zukaitis/midi-grid/Images/firmware_structure.png

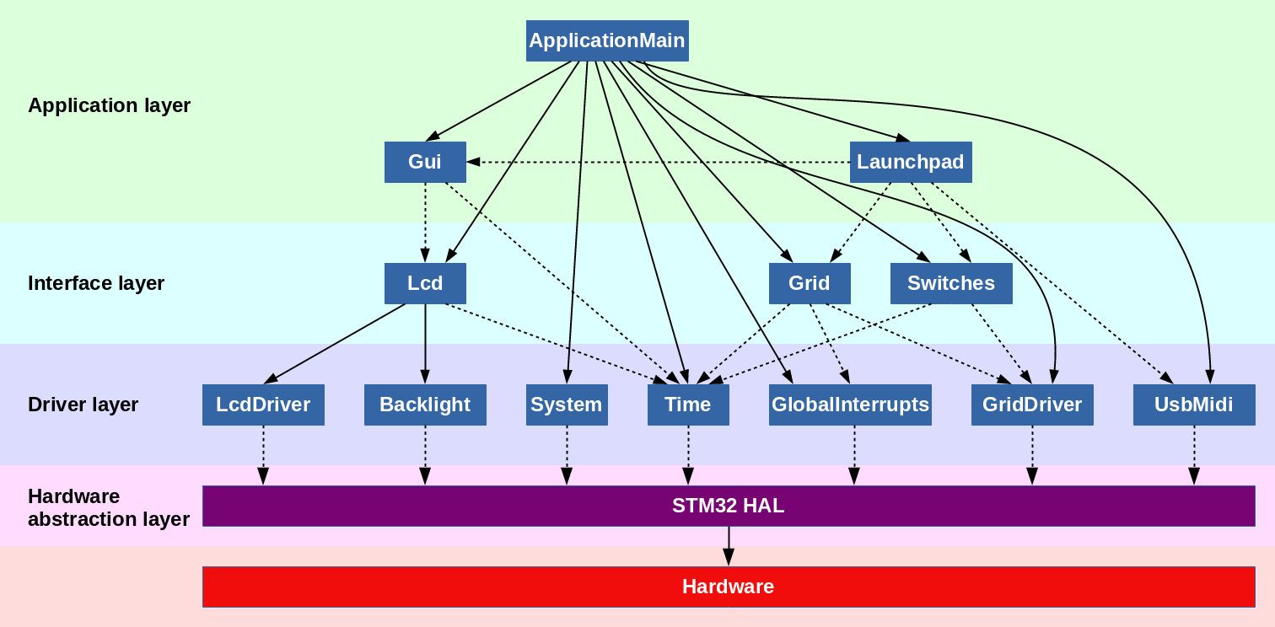
Images/firmware_structure.png
