zukaitis/midi-grid/Images/live_photo_2.jpg

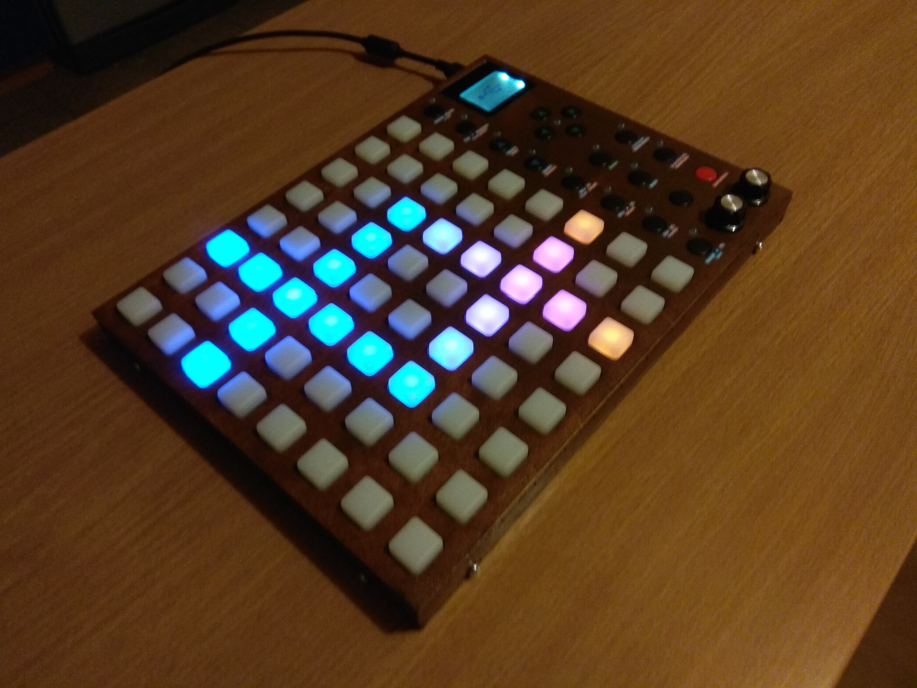
Images/live_photo_2.jpg
