zukaitis/midi-grid/Images/live_photo_3.jpg

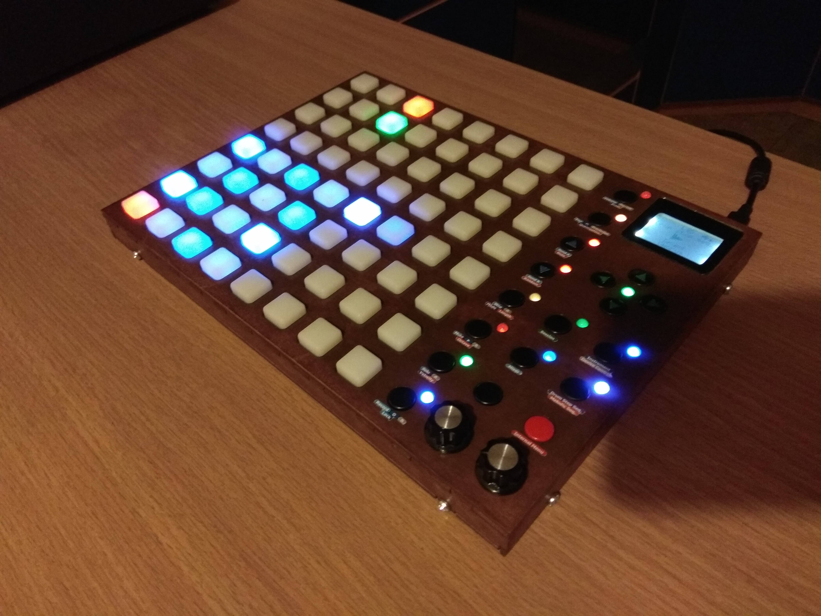
Images/live_photo_3.jpg
