zukaitis/midi-grid/Images/live_photo_5.jpg

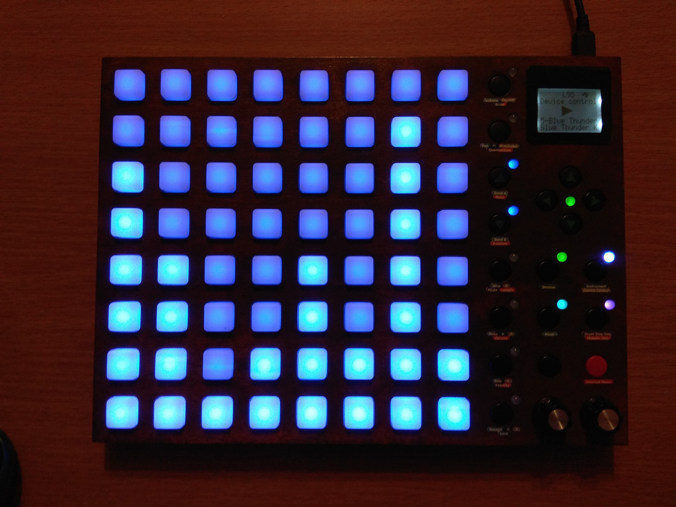
Images/live_photo_5.jpg
