zukaitis/midi-grid/Images/live_photo_6.jpg

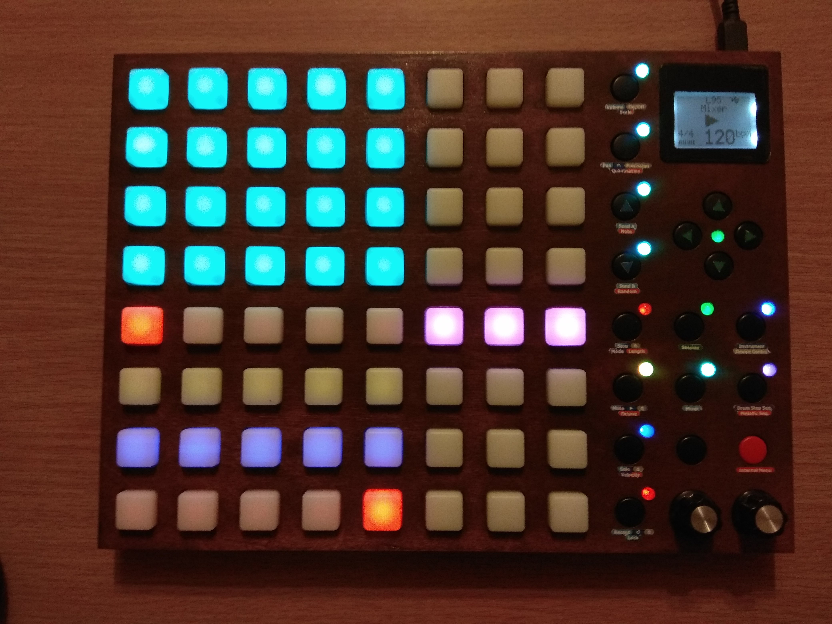
Images/live_photo_6.jpg
