zukaitis/midi-grid/Images/live_photo_7.jpg

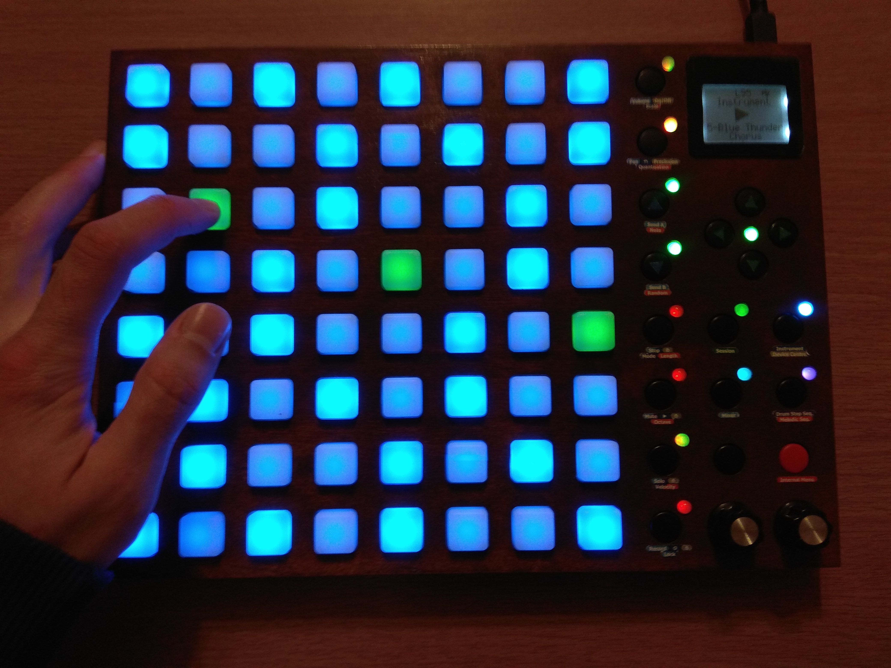
Images/live_photo_7.jpg
