zukaitis/midi-grid/Images/live_photo_9.jpg

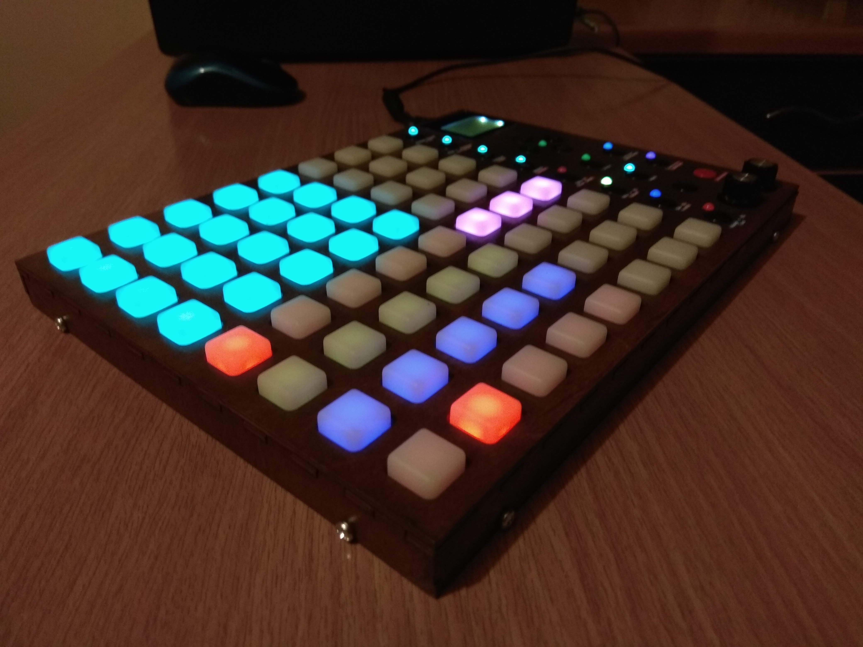
Images/live_photo_9.jpg
