zukaitis/midi-grid/Images/live_photo_10.jpg

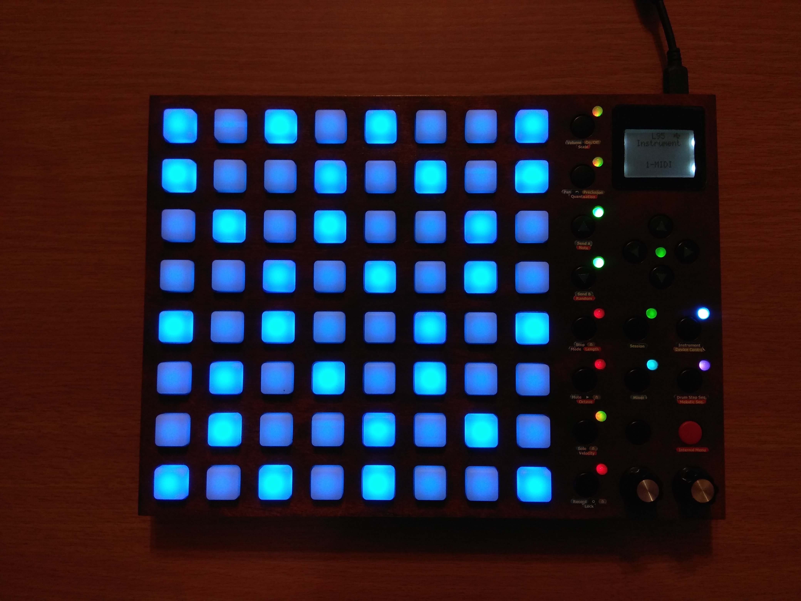
Images/live_photo_10.jpg
