zukaitis/midi-grid/Images/live_photo_11.jpg

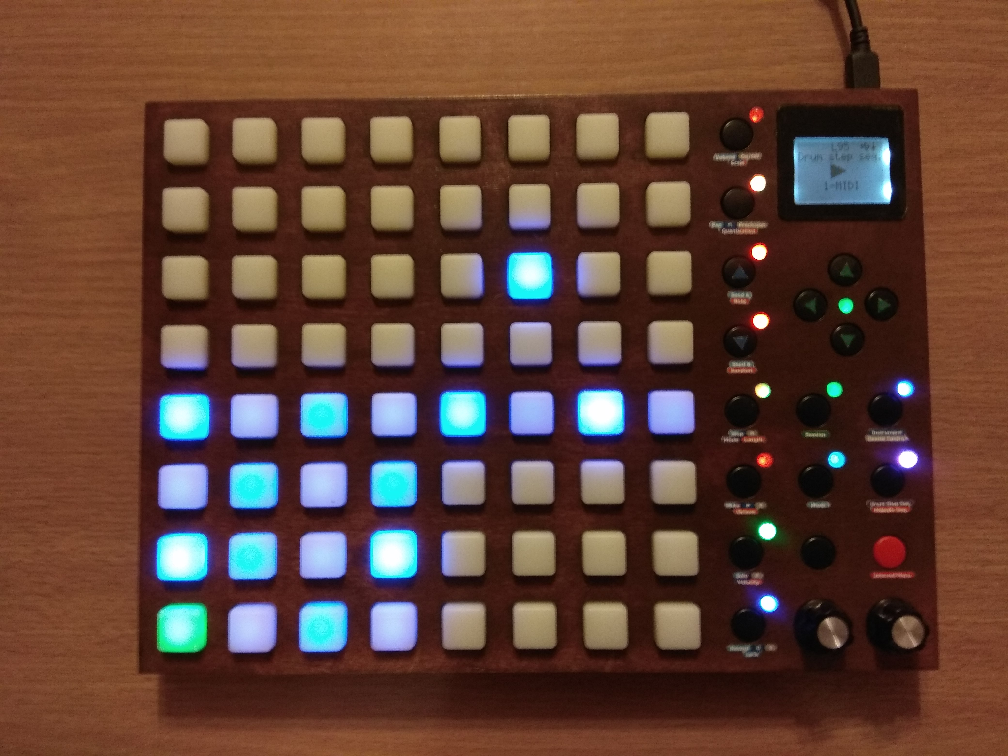
Images/live_photo_11.jpg
