zukaitis/midi-grid/Images/pcb_3d_render_front.png

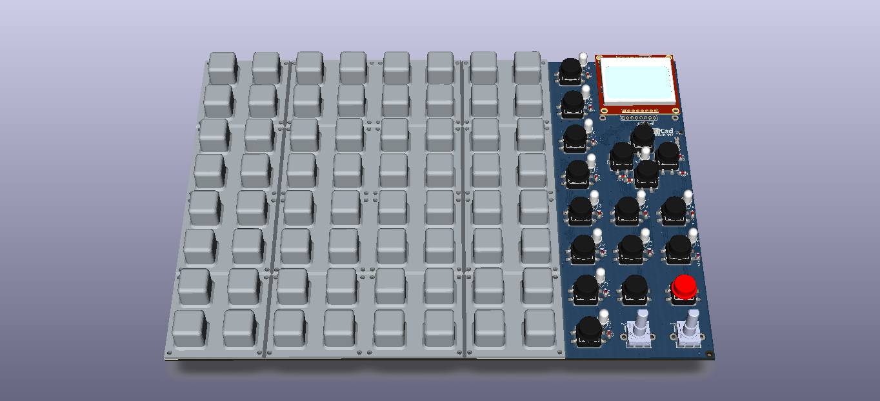
Images/pcb_3d_render_front.png
