zukaitis/midi-grid/Firmware/Src/main.c

/**
  ******************************************************************************
  * @file           : main.c
  * @brief          : Main program body
  ******************************************************************************
  * This notice applies to any and all portions of this file
  * that are not between comment pairs USER CODE BEGIN and
  * USER CODE END. Other portions of this file, whether 
  * inserted by the user or by software development tools
  * are owned by their respective copyright owners.
  *
  * Copyright (c) 2018 STMicroelectronics International N.V. 
  * All rights reserved.
  *
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
  ******************************************************************************
  */
/* Includes ------------------------------------------------------------------*/
#include "main.h"
#include "stm32f4xx_hal.h"

#include "program/launchpad.h"
#include "lcd/lcd.h"
#include "usb/usb_device.h"
#include "usb/queue32.h"

#include "grid_buttons/grid_buttons.h"

ADC_HandleTypeDef hadc1;

//SPI_HandleTypeDef hspi2;
//DMA_HandleTypeDef hdma_spi2_tx;

TIM_HandleTypeDef htim1;
TIM_HandleTypeDef htim2;
TIM_HandleTypeDef htim3;
TIM_HandleTypeDef htim4;

UART_HandleTypeDef huart6;

/* USER CODE BEGIN PV */
uint16_t brightnessTestResult[46000];

extern stB4Arrq rxq;

/* USER CODE END PV */

void SystemClock_Config(void);
static void MX_GPIO_Init(void);
static void MX_DMA_Init(void);
static void MX_SPI2_Init(void);
static void MX_TIM1_Init(void);
static void MX_USART6_UART_Init(void);
static void MX_ADC1_Init(void);

void randomLightAnimation();
void runBrigthnessTest();

void HAL_TIM_MspPostInit(TIM_HandleTypeDef *htim);
                                
/* USER CODE BEGIN PFP */

/* USER CODE END PFP */

/* USER CODE BEGIN 0 */
extern void initialise_monitor_handles(void); // semihosting
/* USER CODE END 0 */

/**
  * @brief  The application entry point.
  *
  * @retval None
  */
int main(void)

{
    volatile uint32_t i=0;
    uint8_t buttonX, buttonY, event, velocity;
  /* MCU Configuration----------------------------------------------------------*/

  /* Reset of all peripherals, Initializes the Flash interface and the Systick. */
  HAL_Init();

  /* Configure the system clock */
  SystemClock_Config();

  /* Initialize all configured peripherals */
  //MX_GPIO_Init();
  //MX_DMA_Init();
  //MX_SPI2_Init();
  //MX_TIM1_Init();
 // MX_USART6_UART_Init();
  MX_USB_DEVICE_Init();
 // MX_ADC1_Init();
  /* Infinite loop */
#ifdef USE_SEMIHOSTING
  initialise_monitor_handles(); // enable semihosting
#endif

  grid_initialize();
  grid_enable();

  LCD_init();
  lcd_printJustified("Been there", 0, 0, Justification_LEFT);
  lcd_printJustified("Done that", LCD_WIDTH, 15, Justification_RIGHT);
  lcd_printJustified("Doing again", LCD_WIDTH/2, 24, Justification_CENTER);
  lcd_printJustified("tomorrow", LCD_WIDTH/2, 31, Justification_CENTER);
  lcd_update();
//  char outstring[4] = {0, 0, 0, 0};
//  while(1)
//  {
//      if (HAL_GetTick() > i)
//      {
//          outstring[0] = i/100000 + 0x30;
//          outstring[1] = i/10000 + 0x30;
//          outstring[2] = i/1000 + 0x30;
//          outstring[3] = 0;
//          lcd_clear();
//          LCD_print(&outstring[0], 16, (i/1000)%48);
//          lcd_update();
//          i = HAL_GetTick() + 1000; //1s
//      }
//  }
  //runBrigthnessTest();
#ifdef USE_SEMIHOSTING
  printf("Semihosting output enabled\n");
#endif

  while (0 == rxq.num)
  {
      //randomLightAnimation();
      if (grid_getButtonEvent(&buttonX, &buttonY, &event))
      {
          if (isUsbConnected())
          {
              velocity = (event) ? 127 : 0;
              sendNoteOn(0,sessionLayout[buttonX][buttonY],velocity);
          }
          break;
      }
  }

  while (!isUsbConnected())
  {
      i++;
  }
#ifdef USE_SEMIHOSTING
  printf("Printing unacknowledged MIDI messages:\n");
#endif
  launchpad_runProgram();

      /* USER CODE END 3 */
}

void randomLightAnimation()
{
    static uint32_t newLightTime = 0;
    static uint8_t ledsChanged = 0;
    uint8_t ledPositionX, ledPositionY;
    uint8_t fullyLitColour;
    struct Colour colour;
    if (HAL_GetTick() >= newLightTime)
    {
        ledPositionX = rand() % 8;
        ledPositionY = rand() % 8;
        fullyLitColour = rand() % 3;
        if (0 == fullyLitColour)
        {
            colour.Red = 64;
            colour.Green = rand() % 65;
            colour.Blue = rand() % 65;
        }
        else if (1 == fullyLitColour)
        {
            colour.Red = rand() % 65;
            colour.Green = 64;
            colour.Blue = rand() % 65;
        }
        else if (2 == fullyLitColour)
        {
            colour.Red = rand() % 65;
            colour.Green = rand() % 65;
            colour.Blue = 64;
        }
        grid_setLedColour(ledPositionX, ledPositionY, &colour);
        newLightTime = HAL_GetTick() + 500 + rand() % 1000;
        ledsChanged++;
        if (ledsChanged > 63)
        {
            grid_setAllLedsOff();
            ledsChanged = 0;
        }
    }
}

void runBrigthnessTest()
{
    volatile uint32_t nextReadoutTime = 0;
    uint16_t result = 0;
    uint16_t i = 0;
    grid_setLedOutputDirectly(0, 0, 1001, 1001, 1001);
    grid_setLedOutputDirectly(1, 0, 1001, 47000, 47000);
    grid_setLedOutputDirectly(2, 0, 47000, 1001, 47000);
    grid_setLedOutputDirectly(3, 0, 47000, 47000, 1001);
    grid_setLedOutputDirectly(9, 4, 47000, 47000, 47000);

    nextReadoutTime = HAL_GetTick() + 10000; // 10s delay at the start
    while (HAL_GetTick() < nextReadoutTime)
    {};

    for (i=47000; i>1000;--i)
    {
        grid_setLedOutputDirectly(9, 4, i, 47000, 47000);
        nextReadoutTime = HAL_GetTick() + 10; // 10ms delay
        while (HAL_GetTick() < nextReadoutTime)
        {};
        HAL_ADC_Start(&hadc1);
        if (HAL_ADC_PollForConversion(&hadc1, 1000) == HAL_OK)
        {
            result = HAL_ADC_GetValue(&hadc1);
            brightnessTestResult[47000-i] = result;
            if (4095 == result)
            {
                break;
            }
        }
    }
}

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
