zukaitis/midi-grid/Firmware/src/hardware/grid/GridDriver.h

#pragma once

#include "hardware/grid/InputInterface.h"
#include "hardware/grid/OutputInterface.h"
#include "hardware/grid/TestingInterface.h"

#include <etl/array.h>
#include <etl/vector.h>
#include <freertos/semaphore.hpp>

namespace hardware
{
namespace grid
{

class GridDriver : public InputInterface, public OutputInterface, public TestingInterface
{
public:
    GridDriver();
    virtual ~GridDriver() = default;

    void addThreadToNotify( freertos::Thread* thread ) override;
    void addSemaphoreToGive( freertos::BinarySemaphore* semaphore ) override;
    const InputDebouncingBuffers& getInputDebouncingBuffers() const override;
    const InputBuffer& getStableInputBuffer() const override;

    void setRedOutput( const Coordinates& coords, uint32_t value ) override;
    void setGreenOutput( const Coordinates& coords, uint32_t value ) override;
    void setBlueOutput( const Coordinates& coords, uint32_t value ) override;

    void setAllOff() override;

    void injectButtonPress( const Coordinates& coords ) override;

    void initialize() const;
    void start() const;

    static void notifyInputReadoutToBuffer0Complete();
    static void notifyInputReadoutToBuffer1Complete();

private:
    void initializeBaseTimer() const;
    void initializeDma() const;
    void initializeGpio() const;
    void initializePwmGpio() const;
    void initializePwmTimers() const;

    static void notifyThreads();

    static uint8_t stableBufferIndex_;
    static InputDebouncingBuffers input_;
    static etl::array<etl::array<uint32_t, numberOfRows>, numberOfColumns> redOutput_;
    static etl::array<etl::array<uint32_t, numberOfRows>, numberOfColumns> greenOutput_;
    static etl::array<etl::array<uint32_t, numberOfRows>, numberOfColumns> blueOutput_;

    static etl::vector<freertos::Thread*, 7> threadToNotify_;
    static etl::vector<freertos::BinarySemaphore*, 4> notificationReplacement_;
};

}
}
