zukaitis/midi-grid/Firmware/src/application/launchpad/Launchpad.hpp

#pragma once

#include "application/Application.hpp"
#include "application/launchpad/LcdGui.hpp"
#include "etl/string_view.h"
#include "testing/TestingInterface.h"
#include "types/Color.h"

#include <etl/array.h>
#include <etl/cstring.h>

namespace grid
{
    class GridInterface;
}

namespace additional_buttons
{
    class AdditionalButtonsInterface;
}

namespace rotary_controls
{
    class RotaryControlsInterface;
}

namespace midi
{
    class UsbMidi;
}

namespace mcu
{
    class System;
}

namespace testing
{
    class TestingInterface;
}

namespace application
{

namespace launchpad
{

enum Layout : uint8_t
{
    Layout_SESSION = 0,
    Layout_USER1,
    Layout_USER2,
    Layout_RESERVED,
    Layout_VOLUME,
    Layout_PAN,
    kMaximumLayoutIndex = Layout_PAN
};

enum class Mode : uint8_t
{
    SESSION = 0,
    INSTRUMENT,
    DEVICE_CONTROLLER,
    USER1,
    DRUM_STEP_SEQUENCER,
    MELODIC_SEQUENCER,
    USER2,
    MIXER,
    UNKNOWN
};

enum Submode : uint8_t
{
    DEFAULT = 0,
    SCALE_INSTRUMENT, // Instrument
    SCALE, // Drum step sequencer
    VOLUME, // Mixer
    PAN, // Mixer
    SEND_A, // Mixer
    SEND_B, // Mixer
    LENGTH, // Melodic step sequencer
    OCTAVE, // Melodic step sequencer
    VELOCITY // Melodic step sequencer
};

class Launchpad : public Application
{
public:
    friend class LcdGui; // allow GUI to read info

    Launchpad( ApplicationController* applicationController, grid::GridInterface* grid,
        additional_buttons::AdditionalButtonsInterface* additionalButtons, rotary_controls::RotaryControlsInterface* rotaryControls,
        lcd::LcdInterface* lcd, midi::UsbMidi* usbMidi, mcu::System* system, testing::TestingInterface* testing );

private:
    void run( ApplicationThread& thread ) override;

    void handleAdditionalButtonEvent( const additional_buttons::Event& event ) override;
    void handleGridButtonEvent( const grid::ButtonEvent& event ) override;
    void handleMidiPacket( const midi::MidiPacket& packet ) override;
    void handleRotaryControlEvent( const rotary_controls::Event& event ) override;

    Mode determineMode();
    Submode determineSubmode();

    void processDawInfoMessage( const etl::string_view& message );
    void processChangeControlMidiMessage( uint8_t channel, uint8_t control, uint8_t value );
    void processNoteOnMidiMessage( uint8_t channel, uint8_t note, uint8_t velocity );
    void processSystemExclusiveMessage( const etl::string_view& message );
    void processSystemExclusiveMidiPacket( const midi::MidiPacket& packet );

    void sendMixerModeControlMessage();

    LcdGui gui_;
    grid::GridInterface& grid_;
    midi::UsbMidi& usbMidi_;
    mcu::System& system_;
    testing::TestingInterface& testing_;

    bool applicationEnded_;
    Mode mode_;
    Submode submode_;
    Layout layout_;
    etl::array<int16_t, 2> rotaryControlValue_;
    bool isPlaying_;
    bool isRecording_;
    bool isSessionRecording_;
    static const uint8_t maximumDawInfoStringLength = 32;
    bool hasClip_;
    etl::string<maximumDawInfoStringLength> clipName_;
    Color clipColor_;
    bool clipIsPlaying_;
    etl::string<maximumDawInfoStringLength> deviceName_;
    etl::string<maximumDawInfoStringLength> trackName_;
    Color trackColor_;
    bool nudgeDownActive_;
    bool nudgeUpActive_;
    uint16_t tempo_;
    uint8_t signatureNumerator_;
    uint8_t signatureDenominator_;

    etl::string<64> systemExclusiveInputMessage_;
};

}  // namespace launchpad
}  // namespace application
