zukaitis/midi-grid/Firmware/src/system/System.hpp

#pragma once

#include <cstdint>

namespace mcu
{

class System
{
public:
    System();
    virtual ~System() = default;

    void initialize();
    bool isUsbConnected();
    void resetIntoBootloader();

    static void delayDirty( uint32_t timeMs );

private:
    void configureNvicPriorities();
    void configureSystemClock();
};

}  // namespace mcu
