zukaitis/midi-grid/Firmware/Src/application/Launchpad.hpp

#ifndef APPLICATION_LAUNCHPAD_HPP_
#define APPLICATION_LAUNCHPAD_HPP_

#include "application/Application.hpp"
#include "Types.h"

namespace grid
{
    class Grid;
    class AdditionalButtons;
    class RotaryControls;
}

namespace lcd
{
    class Gui;
}

namespace midi
{
    class UsbMidi;
}

namespace application
{

enum Layout : uint8_t
{
    Layout_SESSION = 0,
    Layout_USER1,
    Layout_USER2,
    Layout_RESERVED,
    Layout_VOLUME,
    Layout_PAN,
    kMaximumLayoutIndex = Layout_PAN
};

enum Launchpad95Mode : uint8_t
{
    Launchpad95Mode_SESSION = 0,
    Launchpad95Mode_INSTRUMENT,
    Launchpad95Mode_DEVICE_CONTROLLER,
    Launchpad95Mode_USER1,
    Launchpad95Mode_DRUM_STEP_SEQUENCER,
    Launchpad95Mode_MELODIC_SEQUENCER,
    Launchpad95Mode_USER2,
    Launchpad95Mode_MIXER,
    Launchpad95Mode_UNKNOWN
};

enum Launchpad95Submode : uint8_t
{
    Launchpad95Submode_DEFAULT = 0,
    Launchpad95Submode_SCALE, // Instrument and Drum step sequencer
    Launchpad95Submode_VOLUME, // Mixer
    Launchpad95Submode_PAN, // Mixer
    Launchpad95Submode_SEND_A, // Mixer
    Launchpad95Submode_SEND_B, // Mixer
    Launchpad95Submode_LENGTH, // Melodic step sequencer
    Launchpad95Submode_OCTAVE, // Melodic step sequencer
    Launchpad95Submode_VELOCITY // Melodic step sequencer
};

class Launchpad : public Application
{
public:
    Launchpad( ApplicationController& applicationController, grid::Grid& grid, grid::AdditionalButtons& additionalButtons,
        grid::RotaryControls& rotaryControls, lcd::Gui& gui, midi::UsbMidi& usbMidi );

private:
    void run( ApplicationThread& thread );

    void handleAdditionalButtonEvent( const grid::AdditionalButtons::Event event );
    void handleGridButtonEvent( const grid::Grid::ButtonEvent event );
    void handleMidiPacket( const midi::MidiPacket packet );
    void handleRotaryControlEvent( const grid::RotaryControls::Event event );

    Launchpad95Mode determineLaunchpad95Mode();
    Launchpad95Submode determineLaunchpad95Submode();

    void processDawInfoMessage( const char* const message, uint8_t length );
    void processChangeControlMidiMessage( const uint8_t channel, const uint8_t control, const uint8_t value );
    void processNoteOnMidiMessage( uint8_t channel, uint8_t note, uint8_t velocity );
    void processSystemExclusiveMessage( uint8_t* const message, uint8_t length );
    void processSystemExclusiveMidiPacket( const midi::MidiPacket& packet );

    void sendMixerModeControlMessage();
    void setCurrentLayout( const Layout layout );

    grid::Grid& grid_;
    lcd::Gui& gui_;
    midi::UsbMidi& usbMidi_;

    Launchpad95Mode currentLaunchpad95Mode_; // used only to identify submode
    Layout currentLayout_;
    int16_t rotaryControlValue_[2];

    static const uint8_t kSystemExclussiveMessageMaximumLength_ = 64;
    uint8_t systemExclusiveInputMessage_[kSystemExclussiveMessageMaximumLength_];
    uint8_t incomingSystemExclusiveMessageLength_;
};

} // namespace

#endif // APPLICATION_LAUNCHPAD_HPP_
