zukaitis/midi-grid/Firmware/src/hardware/lcd/SpiInterface.h

#pragma once

#include "types/Color.h"
#include <cstdint>
#include <etl/array_view.h>

namespace hardware
{
namespace lcd
{

using RawDataView = etl::array_view<const uint8_t>;

class SpiInterface
{
public:
    virtual ~SpiInterface() = default;

    virtual void initialize() const = 0;
    virtual void setBulkTransferStartAddressIncrement( uint16_t increment ) = 0;

    virtual void reset() const = 0;
    virtual void writeCommand( uint8_t command ) const = 0;
    virtual void writeData( const uint8_t& data, uint32_t size ) const = 0;
    virtual void writeData( const RawDataView& data ) const = 0;
    virtual void writeData( const void* address, uint16_t size ) const = 0;
    virtual void writeData( const void* startAddress, uint16_t segmentSize, uint16_t numberOfSegments ) const = 0;
};

}  // namespace lcd
}  // namespace hardware
