zukaitis/midi-grid/Firmware/generate_build_file.py

#!/usr/bin/python3

from ninja import ninja_syntax
import os
import yaml

def remove_file_extension( filename: str ) -> str:
    (root, _extension) = os.path.splitext( filename )
    return root

def extract_extension( filename: str ) -> str:
    (_root, extension) = os.path.splitext( filename )
    return extension

BUILD_FILENAME = 'build.ninja'
ninja_writer = ninja_syntax.Writer( open( BUILD_FILENAME, 'w' ) )
n = ninja_writer

SETTINGS_FILENAME = 'build_settings.yaml'
with open( SETTINGS_FILENAME, 'r') as read_file:
    settings = yaml.load( read_file, Loader=yaml.BaseLoader )

SCRIPT_NAME = os.path.basename( __file__ )

n.comment( 'This file is generated using ' + SCRIPT_NAME + ' script, do not edit it by hand!' )
n.comment( 'Settings are parsed from ' + SETTINGS_FILENAME + ' file' )
n.newline()

n.variable( 'ninja_required_version', '1.8' )
n.newline()

n.comment( 'Directory, which will store all .o and .d files' )
out_dir = ''
if 'output_directory' in settings:
    out_dir = settings['output_directory']
    if out_dir[-1] != '/' or '\\':
        out_dir += '/'
n.variable( 'out_dir', out_dir )
n.newline()

n.comment( 'Primary target file' )
n.variable( 'target', settings['target'] )
n.newline()

n.comment( 'Compilers and utilities to be used in the build' )
n.variable( 'cc', settings['c_compiler'] )
n.variable( 'cxx', settings['cxx_compiler'] )
n.variable( 'as', settings['asm_compiler'] )
n.variable( 'ld', settings['linker'] )
n.variable( 'objcopy', settings['object_copy_utility'] )
n.variable( 'objdump', settings['object_information_utility'] )
n.variable( 'size', settings['output_size_report_utility'] )
n.variable( 'dfu', settings['dfu_conversion_utility'] )
n.newline()

n.comment( 'Build flags' )
n.variable( 'arch_flags', settings['arch_flags'] )
n.variable( 'c_flags', settings['c_flags'] )
n.variable( 'cxx_flags', settings['cxx_flags'] )

inc_flags = list( '-I' + i for i in settings['include_directories'] )
n.variable( 'inc_flags', inc_flags )

ld_flags = settings['linker_flags']
ld_flags.append( '-T ' + settings['linker_script'] )

# if .map file is required, add linker flag to generate it
for ao in settings['additional_outputs']:
    extension = extract_extension( ao )
    if '.map' == extension:
        ld_flags.append( '-Wl,-Map=' + ao )

n.variable( 'ld_flags', ld_flags )
n.newline()

n.comment( 'Rules for different types of inputs and outputs' )
n.rule( 'as',
    command='$as -MMD $arch_flags $c_flags -c $in -o $out',
    description='AS $out' )
n.newline()

n.rule( 'cc',
    command='$cc -MMD -MT $out -MF $out.d $arch_flags $c_flags $inc_flags -c $in -o $out',
    depfile='$out.d',
    description='CC $out' )
n.newline()

n.rule( 'cxx',
    command='$cxx -MMD -MT $out -MF $out.d $arch_flags $c_flags $cxx_flags $inc_flags -c $in -o $out',
    depfile='$out.d',
    description='CXX $out' )
n.newline()

n.rule( 'link',
    command='$ld $arch_flags $ld_flags -o $out $in $libs',
    description='LINK $out' )
n.newline()

n.rule( 'size',
    command='$size $in | tee $out',
    description='Size report' )
n.newline()

n.rule( 'bin',
    command='$objcopy -O binary $in $out',
    description='BIN $out' )
n.newline()

n.rule( 'hex',
    command='$objcopy -O ihex $in $out',
    description='HEX $out' )
n.newline()

n.comment( 'DFU build generates temporary .hex file from target and deletes it after .dfu output is generated' )
n.rule( 'dfu',
    command='$objcopy -O ihex $in temp.hex && $dfu -i temp.hex $out && rm temp.hex',
    description='HEX $out' )
n.newline()

n.comment( 'Regenerate build files if build script changes.' )
n.rule( 'configure',
    command='python3 ' + SCRIPT_NAME,
    generator=True,
    description='Generating $out file' )
n.newline()

n.rule( 'compdb',
    command='ninja -t compdb cxx cc > $out',
    description='Generating $out file' )
n.newline()

objs = list()

n.comment( 'Instructions to build each file' )
for f in settings['asm_source_files']:
    o = out_dir + remove_file_extension( f ) + '.o'
    n.build( o, 'as', f )
    objs.append( o )
n.newline()

for f in settings['c_source_files']:
    o = out_dir + remove_file_extension( f ) + '.o'
    n.build( o, 'cc', f )
    objs.append( o )
n.newline()

for f in settings['cxx_source_files']:
    o = out_dir + remove_file_extension( f ) + '.o'
    n.build( o, 'cxx', f )
    objs.append( o )
n.newline()

n.comment( 'Target linker instruction' )
n.build( '$target', 'link', objs )
n.newline()

n.comment( 'Size report instruction' )
n.build( '$out_dir/size.txt', 'size', '$target' )
n.newline()

n.comment( 'Generate compilation database' )
n.build( 'compile_commands.json', 'compdb' )
n.newline()

additional_output_instructions = ''
for ao in settings['additional_outputs']:
    extension = extract_extension( ao )
    if '.bin' == extension:
        n.build( ao, 'bin', '$target' )
        additional_output_instructions += ' ' + ao
    elif '.hex' == extension:
        n.build( ao, 'hex', '$target' )
        additional_output_instructions += ' ' + ao
    elif '.dfu' == extension:
        n.build( ao, 'dfu', '$target' )
        additional_output_instructions += ' ' + ao

n.build( BUILD_FILENAME, 'configure', implicit=[SCRIPT_NAME, SETTINGS_FILENAME] )

n.build( 'all', 'phony ' + BUILD_FILENAME + ' $target $out_dir/size.txt compile_commands.json' + additional_output_instructions )
n.default( 'all' )
