zukaitis/midi-grid/Firmware/src/application/launchpad/Images.hpp

#pragma once

#include <etl/array.h>
#include <cstdint>

namespace application
{
namespace launchpad
{

static const etl::array<uint8_t, 9> usbSymbolSmallArray = { 0x1C, 0x1C, 0x08, 0x0E, 0x3B, 0x6A, 0x68, 0x1C, 0x08 };

static const etl::array<uint8_t, 8> midiSymbolSmallArray = { 0x1C, 0x36, 0x7F, 0x1D, 0x1D, 0x7F, 0x36, 0x1C };

static const etl::array<uint8_t, 5> arrowSmallUpArray = { 0x04, 0x06, 0x7F, 0x06, 0x04 };

static const etl::array<uint8_t, 5> arrowSmallDownArray = { 0x10, 0x30, 0x7F, 0x30, 0x10 };

static const etl::array<uint8_t, 32> playArray = {
        0xFE, 0xFC, 0xFC, 0xFC, 0xF8, 0xF8, 0xF0, 0xF0, 0xF0, 0xE0, 0xE0, 0xC0, 0xC0, 0xC0, 0x80, 0x80,
        0x3F, 0x1F, 0x1F, 0x1F, 0x0F, 0x0F, 0x07, 0x07, 0x07, 0x03, 0x03, 0x01, 0x01, 0x01, 0x00, 0x00
};

static const etl::array<uint8_t, 32> recordingOnArray = {
        0xE0, 0xF0, 0xF8, 0xFC, 0xFC, 0xFE, 0xFE, 0xFE, 0xFE, 0xFE, 0xFE, 0xFC, 0xFC, 0xF8, 0xF0, 0xE0,
        0x03, 0x07, 0x0F, 0x1F, 0x1F, 0x3F, 0x3F, 0x3F, 0x3F, 0x3F, 0x3F, 0x1F, 0x1F, 0x0F, 0x07, 0x03
};

static const etl::array<uint8_t, 36> sessionRecordingOnArray = {
        0xE0, 0xF0, 0x38, 0x1C, 0x0C, 0x06, 0x06, 0x06, 0x06, 0x06, 0x06, 0x0C, 0x1C, 0x38, 0xF0, 0xE0,
        0x03, 0x07, 0x0E, 0x1C, 0x18, 0x30, 0x30, 0x30, 0x30, 0x30, 0x30, 0x18, 0x1C, 0x0E, 0x07, 0x03
};

static const etl::array<uint8_t, 10> nudgeDownInactiveArray = { 0x00, 0x3C, 0x3C, 0x00, 0x3C, 0x00, 0x3C, 0x00, 0x3C, 0x00 };

static const etl::array<uint8_t, 10> nudgeDownActiveArray = { 0xFF, 0xC3, 0xC3, 0xFF, 0xC3, 0xFF, 0xC3, 0xFF, 0xC3, 0xFF };

static const etl::array<uint8_t, 10> nudgeUpInactiveArray = { 0x00, 0x3C, 0x00, 0x3C, 0x00, 0x3C, 0x00, 0x3C, 0x3C, 0x00 };

static const etl::array<uint8_t, 10> nudgeUpActiveArray = { 0xFF, 0xC3, 0xFF, 0xC3, 0xFF, 0xC3, 0xFF, 0xC3, 0xC3, 0xFF };

}  // namespace launchpad

}  // namespace application
