zukaitis/midi-grid/Firmware/Src/lcd/images.h

/*
 * images.h
 *
 *  Created on: 2018-03-12
 *      Author: Gedas
 */

#ifndef LCD_IMAGES_H_
#define LCD_IMAGES_H_

namespace lcd
{

static const uint8_t usbLogoArray[180] = {
        0x00, 0x00, 0x00, 0x00, 0x00, 0x00, 0x00, 0x00, 0x00, 0x00, 0x00, 0x00, 0x00, 0x00, 0x00, 0x00,
        0x00, 0x00, 0x00, 0x00, 0x00, 0x80, 0xC0, 0xE0, 0x70, 0x38, 0x18, 0x18, 0x18, 0x18, 0x18, 0x18,
        0x18, 0x18, 0x3C, 0x7E, 0x7E, 0x7E, 0x3C, 0x18, 0x00, 0x00, 0x00, 0x00, 0x00, 0x00, 0x00, 0x00,
        0x00, 0x00, 0x00, 0x00, 0x00, 0x00, 0x00, 0x00, 0x00, 0x00, 0x00, 0x00, 0x00, 0x00, 0x3C, 0x7E,
        0xFF, 0xFF, 0xFF, 0xFF, 0xFF, 0xFF, 0x7E, 0x3C, 0x18, 0x18, 0x18, 0x18, 0x18, 0x18, 0x1C, 0x1E,
        0x1F, 0x1B, 0x19, 0x18, 0x18, 0x18, 0x38, 0x78, 0xF8, 0xD8, 0x98, 0x18, 0x18, 0x18, 0x18, 0x18,
        0x18, 0x18, 0x18, 0x18, 0x18, 0x18, 0x18, 0x18, 0x18, 0x18, 0x18, 0x18, 0x18, 0x18, 0x18, 0x7E,
        0x7E, 0x3C, 0x3C, 0x18, 0x18, 0x00, 0x00, 0x00, 0x00, 0x00, 0x00, 0x00, 0x00, 0x00, 0x00, 0x00,
        0x00, 0x00, 0x00, 0x00, 0x00, 0x00, 0x00, 0x00, 0x00, 0x00, 0x00, 0x00, 0x00, 0x00, 0x00, 0x00,
        0x00, 0x00, 0x00, 0x00, 0x00, 0x01, 0x03, 0x07, 0x0E, 0x1C, 0x18, 0x18, 0x18, 0x18, 0x18, 0x18,
        0x18, 0x7E, 0x7E, 0x7E, 0x7E, 0x7E, 0x7E, 0x00, 0x00, 0x00, 0x00, 0x00, 0x00, 0x00, 0x00, 0x00,
        0x00, 0x00, 0x00, 0x00
};

}
#endif /* LCD_IMAGES_H_ */
