zukaitis/midi-grid/Firmware/Src/hal/GlobalInterrupts.cpp

#include "hal/GlobalInterrupts.h"

#include "stm32f4xx_hal.h"

namespace hal
{

GlobalInterrupts::GlobalInterrupts()
{
}

GlobalInterrupts::~GlobalInterrupts()
{
}

void GlobalInterrupts::disable()
{
    __disable_irq();
}

void GlobalInterrupts::enable()
{
    __enable_irq();
}

} // namespace hal
