zukaitis/midi-grid/Firmware/Src/hal/GlobalInterrupts.h

#ifndef SYSTEM_GLOBALINTERRUPTS_H_
#define SYSTEM_GLOBALINTERRUPTS_H_

namespace hal {

class GlobalInterrupts
{
public:
    GlobalInterrupts();
    virtual ~GlobalInterrupts();

    void disable();
    void enable();
};

} // namespace hal

#endif /* SYSTEM_GLOBALINTERRUPTS_H_ */
