zukaitis/midi-grid/Firmware/src/hardware/grid/TestingInterface.h

#pragma once

#include "types/Coordinates.h"

namespace hardware
{
namespace grid
{

class TestingInterface
{
public:
    virtual ~TestingInterface() = default;
    virtual void injectButtonPress( const Coordinates& coords ) = 0;
};

}  // namespace grid
}  // namespace hardware
